max05210238/CryptoBar/docs/images/product/boot_screen_blue_led.jpeg

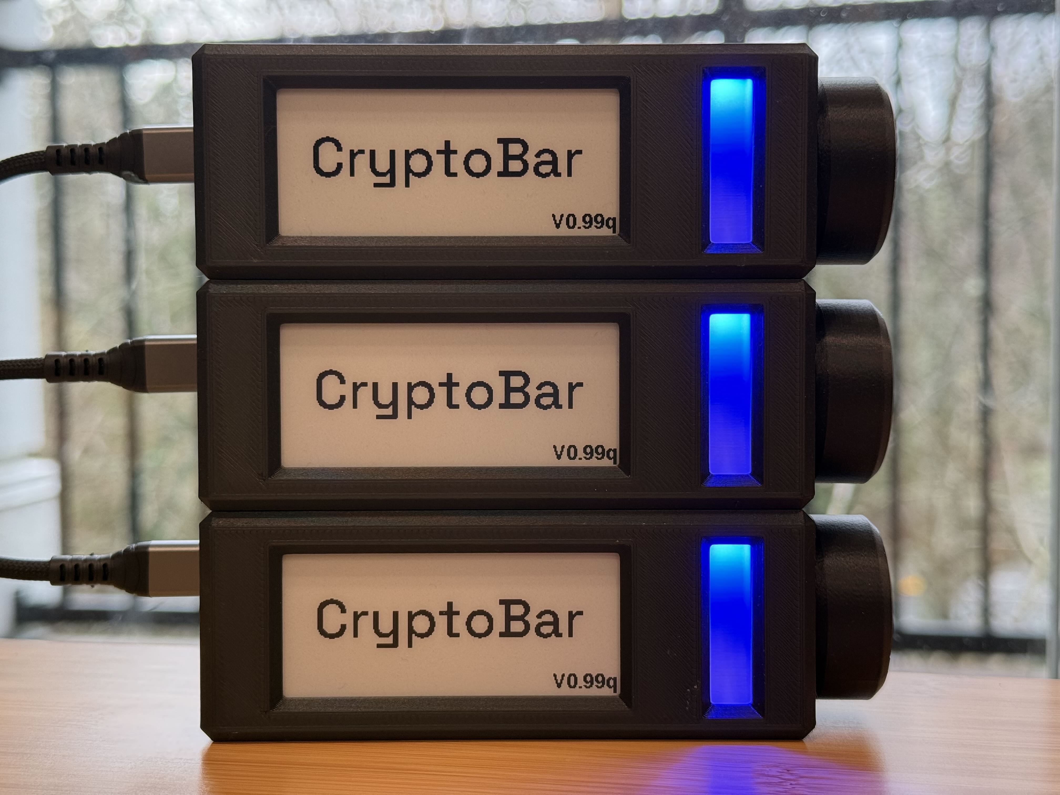
docs/images/product/boot_screen_blue_led.jpeg
