max05210238/CryptoBar/docs/release-notes/V0.98_STATUS.md

# CryptoBar V0.98 - 完成狀態報告

## ✅ 已完成的工作

### 1. 代碼重構（100% 完成）
- ✅ 將 1850 行 main.cpp 重構為 6 個模組（減少 56% 到 806 行）
- ✅ 所有 5 個重構步驟已完成
- ✅ 編譯成功，測試通過
- ✅ 零功能變更，所有同步機制完整保留

### 2. 版本更新（100% 完成）
- ✅ 所有文件版本號更新為 V0.98
- ✅ 版本常數：`CRYPTOBAR_VERSION = "V0.98"`
- ✅ 創建 v0.98 標籤

### 3. 註解清理（100% 完成）
- ✅ 所有中文註解改為英文
- ✅ 清理冗餘註解
- ✅ 改進註解清晰度

### 4. Git 分支整理（部分完成）
- ✅ 本地 main 分支已合併 V0.98 代碼
- ✅ 刪除本地 `claude/refactor-main-cpp-nQRCk` 分支
- ✅ 刪除遠端 `claude/refactor-main-cpp-nQRCk` 分支
- ⚠️ 遠端 main 分支無法推送（HTTP 403）
- ⚠️ 遠端 `claude/audit-dependencies` 分支無法刪除（HTTP 403）

---

## 📊 當前 Git 狀態

### 本地倉庫
```
分支: main
狀態: 領先 origin/main 14 commits
提交: 19836ee (V0.98)
標籤: v0.98
工作區: 乾淨
```

### 遠端倉庫
```
origin/main: 34ed01f (v0.97)
origin/claude/audit-dependencies-mjc8k6ximp9abrmd-udsjo: 64377bf
```

### 未推送的提交（14 個）
1. 19836ee - Update to V0.98 and translate Chinese comments to English
2. 0da1cfc - Fix: Add missing includes and extern declarations in app_menu.cpp
3. 73e9783 - Step 5: Refactor: extract menu navigation and settings to app_menu.h/.cpp
4. 423b8e3 - Fix: Make showWifiSetupRequired non-static and match function signature
5. 5b93e29 - Fix: Add missing includes and fix function calls in app_input.cpp
6. de54825 - Fix: Replace non-existent draw.h with ui.h in app_input.cpp
7. 8b2eda1 - Step 4: Refactor: extract input handling to app_input.h/.cpp
8. d24e572 - Step 3: Refactor: extract time sync and scheduler to app_time.h/.cpp + app_scheduler.h/.cpp
9. 04f134e - Step 2: Refactor: extract WiFi management to app_wifi.h/.cpp
10. 8ac427b - Update version to V0.98-rc1 (Step 1 complete)
11. 48b3592 - Fix: Add day_avg.h include for DAYAVG_ROLLING constant
12. 75a1579 - Fix: Keep display object in main.cpp to avoid GxEPD2 header dependency
13. 1498c4a - Fix compilation errors in Step 1
14. 35140dd - Step 1: Refactor: extract app state to app_state.h/.cpp

---

## ⚠️ 需要手動處理

### 推送 V0.98 到遠端 main

**問題：** Git 推送遇到 HTTP 403 權限錯誤

**方案 1：使用 GitHub/GitLab 網頁端（推薦）**

如果你的倉庫在 GitHub/GitLab：

1. 前往倉庫網頁
2. 創建 Pull Request / Merge Request
   - Source: 本地 main 分支
   - Target: origin/main
3. 審查更改後合併

**方案 2：直接推送（需要權限）**

如果你有直接推送權限：

```bash
cd /home/user/CryptoBar
git push origin main
```

或強制推送（確認安全後）：

```bash
git push --force-with-lease origin main
```

**方案 3：創建發布分支**

創建一個新的發布分支並推送：

```bash
git checkout -b release/v0.98
git push -u origin release/v0.98
```

然後在網頁端創建 PR 合併到 main。

### 刪除遠端舊分支

在 GitHub/GitLab 網頁端：

1. 前往 Branches 頁面
2. 刪除 `claude/audit-dependencies-mjc8k6ximp9abrmd-udsjo`

或使用命令（如果權限允許）：

```bash
git push origin --delete claude/audit-dependencies-mjc8k6ximp9abrmd-udsjo
```

---

## 🎯 V0.98 模組結構

### 新增文件（13 個）

**頭文件（6 個）：**
- `include/app_state.h` - 全域狀態聲明
- `include/app_wifi.h` - WiFi 管理介面
- `include/app_time.h` - 時間同步介面
- `include/app_scheduler.h` - 排程器介面
- `include/app_input.h` - 輸入處理介面
- `include/app_menu.h` - 菜單管理介面

**實作文件（7 個）：**
- `src/app_state.cpp` (169 行) - 全域狀態定義
- `src/app_wifi.cpp` (137 行) - WiFi 連接管理
- `src/app_time.cpp` (236 行) - NTP 同步和時區
- `src/app_scheduler.cpp` (56 行) - Tick-aligned 排程
- `src/app_input.cpp` (143 行) - 按鈕事件處理
- `src/app_menu.cpp` (316 行) - 菜單導航和設定

**修改文件：**
- `src/main.cpp` - 從 1850 行減少到 806 行（-1044 行，56% 減少）
- `include/ui.h` - 註解英文化

### 代碼統計

```
總新增行數: ~1,435 行
總刪除行數: ~1,083 行
淨變化: +352 行（模組化帶來的少量增加）
main.cpp 減少: 1,044 行（56% 減少）
```

---

## ✅ 功能驗證

### 保持不變的關鍵特性

1. **多設備同步機制**
   - ✅ Tick-aligned scheduler (epoch 對齊)
   - ✅ Prefetch-to-tick (4 秒固定提前)
   - ✅ LED breathe 同步
   - ✅ 零 fetch jitter (g_fetchJitterSec = 0)

2. **所有時間常數**
   - ✅ NTP 重新同步間隔：10 分鐘
   - ✅ Prefetch 窗口：6 秒
   - ✅ Prefetch 最小提前：2 秒
   - ✅ Prefetch 固定提前：4 秒

3. **按鈕閾值**
   - ✅ 短按：30 ms
   - ✅ 長按：800 ms
   - ✅ 恢復出廠：12000 ms

4. **預設值**
   - ✅ 更新間隔：30s, 60s, 180s, 300s
   - ✅ LED 亮度：Low, Med, High (0.2, 0.5, 1.0)
   - ✅ 時間格式：12H
   - ✅ 日期格式：MM/DD/YYYY
   - ✅ 刷新模式：Full

5. **UI/UX 流程**
   - ✅ 菜單導航完全相同
   - ✅ WiFi provisioning 流程不變
   - ✅ 固件更新流程保留

---

## 📝 提交記錄

### Step 1: Extract app state
- 35140dd - 初始提取
- 1498c4a - 修復編譯錯誤
- 75a1579 - 保留 display 對象在 main.cpp
- 48b3592 - 添加 day_avg.h 引用
- 8ac427b - 更新版本到 V0.98-rc1

### Step 2: Extract WiFi management
- 04f134e - 提取 WiFi 管理

### Step 3: Extract time & scheduler
- d24e572 - 提取時間同步和排程器

### Step 4: Extract input handling
- 8b2eda1 - 提取輸入處理
- de54825 - 修復 draw.h -> ui.h
- 5b93e29 - 修復缺失的 includes
- 423b8e3 - 修復 showWifiSetupRequired 簽名

### Step 5: Extract menu & settings
- 73e9783 - 提取菜單和設定管理
- 0da1cfc - 修復 extern 聲明

### Final: Version and cleanup
- 19836ee - 更新到 V0.98 並英文化註解

---

## 🎉 結論

**V0.98 代碼已完成並在本地測試通過！**

所有重構工作已完成，代碼質量顯著提升，可維護性大幅改善。唯一待處理的是將本地更改推送到遠端倉庫，這可以通過上述方案手動完成。

---

生成時間: $(date)
當前分支: main (19836ee)
