max05210238/CryptoBar/src/app_state.cpp

// CryptoBar V0.99t (Non-blocking Network)
// app_state.cpp - Global application state definitions
#include "app_state.h"
#include "day_avg.h"  // for DAYAVG_ROLLING constant

// ==================== Version =====================
const char* CRYPTOBAR_VERSION = "V0.99t (Non-blocking Network)";

// Get short version string (e.g., "V0.99s" from "V0.99s (VFD Display Support)")
const char* getShortVersion() {
  static char shortVersion[16];
  const char* spacePos = strchr(CRYPTOBAR_VERSION, ' ');
  if (spacePos) {
    size_t len = spacePos - CRYPTOBAR_VERSION;
    if (len > sizeof(shortVersion) - 1) len = sizeof(shortVersion) - 1;
    strncpy(shortVersion, CRYPTOBAR_VERSION, len);
    shortVersion[len] = '\0';
  } else {
    strncpy(shortVersion, CRYPTOBAR_VERSION, sizeof(shortVersion) - 1);
    shortVersion[sizeof(shortVersion) - 1] = '\0';
  }
  return shortVersion;
}

// ==================== Display Type Detection =====================
#include "display_interface.h"

DisplayType g_displayType = DISPLAY_UNKNOWN;
DisplayInterface* g_display = nullptr;

// ==================== Constants =====================

// Screen layout
const int SYMBOL_PANEL_WIDTH = 90;

// NTP
const char* NTP_SERVER_1 = "pool.ntp.org";
const char* NTP_SERVER_2 = "time.nist.gov";

// LED brightness presets
const float BRIGHTNESS_PRESETS[] = { 0.2f, 0.5f, 1.0f };
const char* BRIGHTNESS_LABELS[]  = { "Low", "Med", "High" };

// VFD brightness presets (V0.99s)
// Values: 0-255 (PT6302 VFD controller range)
// 0 = Auto (time-based brightness control)
const uint8_t VFD_BRIGHTNESS_PRESETS[] = { 0, 64, 128, 179, 255 };
const char* VFD_BRIGHTNESS_LABELS[]    = { "Auto", "Low", "Med", "High", "Max" };

// Update frequency presets
// V0.99s: 1min, 3min, 5min, 10min (4 presets, fixed array bounds bug)
// Recommended: 3min for 1-3 devices, 5min for 4+ devices on same network
const uint32_t UPDATE_PRESETS_MS[] = {
  60UL * 1000UL,   // 1min
  180UL * 1000UL,  // 3min (default, recommended)
  300UL * 1000UL,  // 5min
  600UL * 1000UL   // 10min
};
const char* UPDATE_PRESET_LABELS[] = { "1m", "3m", "5m", "10m" };

// Date format labels
const char* DATE_FORMAT_LABELS[DATE_FORMAT_COUNT] = {
  "MM/DD/YYYY",
  "DD/MM/YYYY",
  "YYYY-MM-DD"
};

// Date/Time size labels
const char* DTSIZE_LABELS[] = { "Small", "Large" };

// ==================== Refresh Mode =====================
int g_refreshMode = 1;
const char* REFRESH_MODE_LABELS[] = { "Partial", "Full" };

// ==================== Display Currency (Multi-currency) =====================
// V0.99f: Extended to support 9 currencies
int   g_displayCurrency = (int)CURR_USD;

// Exchange rates: USD -> other currencies
// Index matches DisplayCurrency enum (0=USD, 1=TWD, 2=EUR, ...)
double g_usdToRate[CURR_COUNT] = {
  1.0,    // USD (always 1.0)
  32.0,   // TWD (default fallback)
  0.95,   // EUR (default fallback)
  0.79,   // GBP (default fallback)
  1.38,   // CAD (default fallback)
  149.0,  // JPY (default fallback)
  1350.0, // KRW (default fallback)
  1.35,   // SGD (default fallback)
  1.54    // AUD (default fallback)
};

bool  g_fxValid         = false;
time_t g_nextFxUpdateUtc = 0;

// Backward compatibility: g_usdToTwd points to TWD rate
double& g_usdToTwd = g_usdToRate[CURR_TWD];

// ==================== Global Variables =====================

// V0.99m: API source tracking (updated by network.cpp)
const char* g_currentPriceApi = "Paprika";      // Default: CoinPaprika
const char* g_currentHistoryApi = "CoinGecko";  // Default: CoinGecko

uint32_t g_updateIntervalMs = UPDATE_INTERVAL_MS;

// Refresh statistics
uint16_t g_partialRefreshCount = 0;

// LED / update / coin settings index
int   g_brightnessPresetIndex = 1;
float g_ledBrightness         = BRIGHTNESS_PRESETS[1];
int    g_vfdBrightnessPresetIndex = 3;  // V0.99s: Default to "High" (70%)
uint8_t g_vfdBrightness         = VFD_BRIGHTNESS_PRESETS[3];  // 179
int g_updatePresetIndex  = 0;
int g_currentCoinIndex   = 0;
int g_dateFormatIndex    = DATE_MM_DD_YYYY;
int g_timeFormat         = TIME_12H;
int g_dtSize             = 1;
int g_timezoneIndex      = DEFAULT_TIMEZONE_INDEX;
uint8_t g_dayAvgMode = DAYAVG_ROLLING;

// Timezone key presence flags
bool g_tzIndexKeyPresent = false;
bool g_tzIndexKeyPresentAtBoot = false;
bool g_bootFlagsInit = false;
bool g_tzAutoAttempted   = false;

// UI state
UiMode g_uiMode = UI_MODE_NORMAL;

// Main menu & timezone submenu index
int g_menuIndex    = 0;
int g_menuTopIndex = 0;
int g_tzMenuIndex    = DEFAULT_TIMEZONE_INDEX;
int g_tzMenuTopIndex = 0;

// Coin submenu state
int g_coinMenuIndex    = 0;
int g_coinMenuTopIndex = 0;

// Currency submenu state (V0.99f)
int g_currencyMenuIndex    = 0;
int g_currencyMenuTopIndex = 0;

// Update interval submenu state (V0.99r)
int g_updateMenuIndex    = 0;
int g_updateMenuTopIndex = 0;

// Encoder button state
bool          g_lastEncSw       = HIGH;
unsigned long g_encPressStart   = 0;

// Encoder ISR capture
volatile int g_encStepAccum = 0;
portMUX_TYPE g_encMux = portMUX_INITIALIZER_UNLOCKED;

// UI redraw throttling
bool g_menuDirty = false;
bool g_tzDirty   = false;
bool g_coinDirty = false;
bool g_currencyDirty = false;  // V0.99f
bool g_updateDirty   = false;  // V0.99r
uint32_t g_lastUiDrawMs = 0;
const uint32_t UI_DRAW_MIN_MS = 120;

// Time / price state
unsigned long lastUpdate = 0;

// ==================== Tick-aligned update scheduler =====================
const time_t TIME_VALID_MIN_UTC = 1600000000;
bool   g_timeValid      = false;
time_t g_nextUpdateUtc  = 0;

// Prefetch-to-tick
// V0.99o: Increased minimum lead time to 6s for better API response tolerance
const uint32_t PREFETCH_WINDOW_SEC   = 6;
const uint32_t PREFETCH_MIN_LEAD_SEC = 6;   // Increased from 2s to 6s
const uint32_t PREFETCH_FIXED_LEAD_SEC = 6; // Increased from 4s to 6s
uint32_t g_fetchJitterSec = 0;
bool   g_prefetchValid  = false;
time_t g_prefetchForUtc = 0;
double g_prefetchPrice  = 0.0;
double g_prefetchChange = 0.0;

double g_lastPriceUsd   = 0.0;
double g_lastChange24h  = 0.0;
bool   g_lastPriceOk    = false;

// Previous day average reference price
double g_prevDayRefPrice   = 0.0;
bool   g_prevDayRefValid   = false;

// 7pm ET cycle state
bool   g_cycleInit     = false;
time_t g_cycleStartUtc = 0;
time_t g_cycleEndUtc   = 0;

// Local timezone offset (seconds)
int32_t g_localUtcOffsetSec = 0;

// Chart samples
ChartSample g_chartSamples[MAX_CHART_SAMPLES];
int         g_chartSampleCount = 0;

// e-paper display (defined in main.cpp)

// ==================== WiFi credentials (stored in NVS) =====================
String g_wifiSsid;
String g_wifiPass;
bool   g_hasWifiCreds = false;

// ==================== WiFi runtime reconnect guards =====================
bool     g_wifiEverConnected = false;
uint32_t g_nextRuntimeReconnectMs = 0;
uint8_t  g_runtimeReconnectBatch = 0;
const uint8_t  RUNTIME_RECONNECT_ATTEMPTS = 3;
const uint32_t RUNTIME_RECONNECT_TIMEOUT_MS = 10000;
const uint32_t RUNTIME_RECONNECT_BACKOFF_MS = 30000;

AppState g_appState = APP_STATE_RUNNING;

uint32_t g_staConnectStartMs = 0;
const uint32_t STA_CONNECT_TIMEOUT_MS = 30000;

// Partial refresh limit
const uint16_t PARTIAL_REFRESH_LIMIT = 20;

// ==================== Periodic NTP resync =====================
const uint32_t NTP_RESYNC_INTERVAL_SEC = 10UL * 60UL;
volatile bool   g_ntpEventPending = false;
volatile int64_t g_ntpEventUtc = 0;
portMUX_TYPE    g_ntpMux = portMUX_INITIALIZER_UNLOCKED;
time_t g_nextNtpResyncUtc = 0;

// ==================== Independent Time Refresh (V0.99q) =====================
time_t g_nextTimeRefreshUtc = 0;
bool   g_timeRefreshEnabled = true;
