max05210238/CryptoBar/src/app_menu.cpp

// CryptoBar V0.99t (Non-blocking Network)
// app_menu.cpp - Menu navigation and settings management

#include <Arduino.h>
#include <WiFi.h>
#include "app_menu.h"
#include "app_state.h"
#include "app_wifi.h"
#include "app_time.h"
#include "app_scheduler.h"
#include "settings_store.h"
#include "led_status.h"
#include "coins.h"
#include "day_avg.h"
#include "network.h"
#include "network_task.h"  // V0.99t: Non-blocking network operations
#include "ui.h"
#include "display_vfd.h"  // V0.99s: For VFD menu items

// Forward declarations for functions that remain in main.cpp
extern const CoinInfo& currentCoin();
extern const char* dayAvgModeLabel(uint8_t mode);
extern void updateAvgLineReference(time_t nowUtc);
extern void updateEtCycle();
extern void bootstrapHistoryFromKrakenOHLC();
extern void updateLedForPrice(float change24h, bool priceOk);
extern unsigned long lastUpdate;  // from main.cpp

// ==================== Settings Management =====================

void loadSettings() {
  StoredSettings st;
  settingsStoreLoad(st);

 // Whether tzIndex was explicitly stored in NVS. Used for one-time Auto TZ.
  g_tzIndexKeyPresent = settingsStoreHasTzIndex();
  if (!g_bootFlagsInit) {
    g_tzIndexKeyPresentAtBoot = g_tzIndexKeyPresent;
    g_bootFlagsInit = true;
  }

  int upd   = st.updPreset;
  int bri   = st.briPreset;
  int vfdBri = st.vfdBriPreset;  // V0.99s: VFD brightness
  int coin  = coinIndexFromTicker(st.coinTicker.c_str());
  int tFmt  = st.timeFmt;
  int dFmt  = st.dateFmt;
  int dtSz  = st.dtSize;
  int tzIdx = st.tzIndex;
  int dayLn = st.dayAvg;
  int rf    = st.rfMode;

  int updCount   = UPDATE_PRESETS_COUNT;
  int briCount   = BRIGHTNESS_PRESETS_COUNT;
  int vfdBriCount = VFD_BRIGHTNESS_PRESETS_COUNT;

  if (upd < 0 || upd >= updCount) upd = 0;
  if (bri < 0 || bri >= briCount) bri = 1;
  if (vfdBri < 0 || vfdBri >= vfdBriCount) vfdBri = 3;  // Default: High
  if (coin < 0 || coin >= coinCount()) coin = coinIndexFromTicker(coinDefault().ticker);
  if (tFmt < 0 || tFmt > TIME_12H) tFmt = TIME_12H;
  if (dFmt < 0 || dFmt >= DATE_FORMAT_COUNT) dFmt = DATE_MM_DD_YYYY;
  if (dtSz < 0 || dtSz > 1) dtSz = 1;
  if (tzIdx < 0 || tzIdx >= TIMEZONE_COUNT) tzIdx = DEFAULT_TIMEZONE_INDEX;
  if (dayLn < 0 || dayLn > 2) dayLn = DAYAVG_ROLLING;
  if (rf < 0 || rf > 1) rf = 1;

  g_updatePresetIndex     = upd;
  g_updateIntervalMs      = UPDATE_PRESETS_MS[g_updatePresetIndex];
  g_brightnessPresetIndex = bri;
  g_ledBrightness         = BRIGHTNESS_PRESETS[g_brightnessPresetIndex];
  ledStatusSetMasterBrightness(g_ledBrightness);
  g_vfdBrightnessPresetIndex = vfdBri;  // V0.99s: VFD brightness
  g_vfdBrightness         = VFD_BRIGHTNESS_PRESETS[g_vfdBrightnessPresetIndex];
  g_currentCoinIndex      = coin;
  g_timeFormat            = tFmt;
  g_dateFormatIndex       = dFmt;
  g_dtSize                = dtSz;
  g_timezoneIndex         = tzIdx;
  g_dayAvgMode          = (uint8_t)dayLn;
  g_refreshMode           = rf;

  g_displayCurrency = st.dispCur;
  if (g_displayCurrency < 0 || g_displayCurrency >= (int)CURR_COUNT) g_displayCurrency = (int)CURR_USD;
  applyTimezone();

  Serial.printf("[Settings] Loaded: coin=%s, upd=%s, LED=%s, timeFmt=%s, date=%s, dtSize=%s, tz=%s, dayAvg=%s, refresh=%s, cur=%s\n",
                currentCoin().ticker,
                UPDATE_PRESET_LABELS[g_updatePresetIndex],
                BRIGHTNESS_LABELS[g_brightnessPresetIndex],
                (g_timeFormat == TIME_24H ? "24h" : "12h"),
                DATE_FORMAT_LABELS[g_dateFormatIndex],
                DTSIZE_LABELS[g_dtSize],
                TIMEZONES[g_timezoneIndex].label,
                dayAvgModeLabel(g_dayAvgMode),
                REFRESH_MODE_LABELS[g_refreshMode],
                CURRENCY_INFO[g_displayCurrency].code);
}

void saveSettings() {
  StoredSettings st;
  st.updPreset = g_updatePresetIndex;
  st.briPreset = g_brightnessPresetIndex;
  st.vfdBriPreset = g_vfdBrightnessPresetIndex;  // V0.99s: VFD brightness
  st.coinTicker = String(currentCoin().ticker);
  st.timeFmt   = g_timeFormat;
  st.dateFmt   = g_dateFormatIndex;
  st.dtSize    = g_dtSize;
  st.tzIndex   = g_timezoneIndex;
  st.dayAvg    = (int)g_dayAvgMode;
  st.rfMode    = g_refreshMode;
  st.dispCur   = g_displayCurrency;

  settingsStoreSave(st);

  Serial.printf("[Settings] Saved: coin=%s, upd=%s, LED=%s, timeFmt=%s, date=%s, dtSize=%s, tz=%s, dayAvg=%s, refresh=%s, cur=%s\n",
                currentCoin().ticker,
                UPDATE_PRESET_LABELS[g_updatePresetIndex],
                BRIGHTNESS_LABELS[g_brightnessPresetIndex],
                (g_timeFormat == TIME_24H ? "24h" : "12h"),
                DATE_FORMAT_LABELS[g_dateFormatIndex],
                DTSIZE_LABELS[g_dtSize],
                TIMEZONES[g_timezoneIndex].label,
                dayAvgModeLabel(g_dayAvgMode),
                REFRESH_MODE_LABELS[g_refreshMode],
                CURRENCY_INFO[g_displayCurrency].code);
}

// ==================== Menu Navigation =====================

void leaveMenu() {
  g_uiMode = UI_MODE_NORMAL;
  Serial.println("[Menu] Exit to main");

  // V0.99s: Use display interface for both e-ink and VFD
  if (g_display) {
    g_display->drawMainScreen(true);
  } else {
    // Fallback to e-ink legacy function
    drawMainScreen(g_lastPriceUsd, g_lastChange24h, true);
  }

  g_partialRefreshCount = 0;
  lastUpdate = millis();
}

void enterMenu() {
  g_uiMode       = UI_MODE_MENU;
  g_menuIndex    = 0;
  g_menuTopIndex = 0;
  Serial.println("[Menu] Enter");

  // V0.99s: Use display interface for both e-ink and VFD
  if (g_displayType == DISPLAY_VFD && g_display) {
    g_display->drawMenuScreen();
  } else {
    // E-ink: use legacy UI function
    drawMenuScreen(true);
  }
}

void enterTimezoneSubmenu() {
  g_uiMode         = UI_MODE_TZ_SUB;
 // g_tzMenuIndex is a DISPLAY position (UTC-ordered), not the raw tzIndex.
  g_tzMenuIndex    = tzDisplayPosFromTzIndex(g_timezoneIndex);
  g_tzMenuTopIndex = max(0, g_tzMenuIndex - 2);
  Serial.println("[Menu] Enter TZ submenu");
  drawTimezoneMenu(false);  // Partial refresh
}

// ==================== Menu Item Handlers =====================

void handleTimezoneSelect() {
 // g_tzMenuIndex is a DISPLAY position (UTC-ordered)
  g_timezoneIndex = tzIndexFromDisplayPos(g_tzMenuIndex);
  applyTimezone();
  saveSettings();
  Serial.printf("[Menu] Timezone -> %s (UTC%+d)\n", TIMEZONES[g_timezoneIndex].label, (int)TIMEZONES[g_timezoneIndex].utcOffsetHours);

  g_uiMode = UI_MODE_MENU;
  if (g_displayType == DISPLAY_VFD && g_display) {
    g_display->drawMenuScreen();
  } else {
    drawMenuScreen(false);  // Partial refresh
  }
}

void handleCoinSelect() {
  g_currentCoinIndex = g_coinMenuIndex;
  saveSettings();
  Serial.printf("[Menu] Coin -> %s (index=%d)\n",
                currentCoin().ticker, g_currentCoinIndex);

  // V0.99t: Reset chart / cycle state (non-blocking)
  g_chartSampleCount = 0;
  g_cycleInit        = false;
  g_lastPriceOk      = false;  // Trigger "Loading..." display
  updateEtCycle();

  // V0.99t: Queue async network requests (non-blocking)
  // Network task will fetch history and price in background
  networkTaskRequestHistory(g_currentCoinIndex);
  networkTaskRequestPrice(g_currentCoinIndex);

  // Return to menu immediately (no waiting for network)
  g_uiMode = UI_MODE_MENU;
  if (g_displayType == DISPLAY_VFD && g_display) {
    g_display->drawMenuScreen();
  } else {
    drawMenuScreen(false);  // Partial refresh
  }
}

void handleCurrencySelect() {
  // V0.99f: Apply selected currency and trigger FX update if needed
  g_displayCurrency = g_currencyMenuIndex;

  // Validate range
  if (g_displayCurrency < 0 || g_displayCurrency >= (int)CURR_COUNT) {
    g_displayCurrency = (int)CURR_USD;
  }

  Serial.printf("[Menu] Currency -> %s-%s\n",
                CURRENCY_INFO[g_displayCurrency].symbol,
                CURRENCY_INFO[g_displayCurrency].code);

  // If switching to non-USD currency, trigger immediate FX update
  if (g_displayCurrency != (int)CURR_USD) {
    g_nextFxUpdateUtc = 0;
  }

  saveSettings();

  // Return to main menu
  g_uiMode = UI_MODE_MENU;
  if (g_displayType == DISPLAY_VFD && g_display) {
    g_display->drawMenuScreen();
  } else {
    drawMenuScreen(false);
  }
}

void handleUpdateIntervalSelect() {
  // V0.99r: Apply selected update interval (only when user confirms selection)
  g_updatePresetIndex = g_updateMenuIndex;

  // Validate range
  if (g_updatePresetIndex < 0 || g_updatePresetIndex >= UPDATE_PRESETS_COUNT) {
    g_updatePresetIndex = 0;
  }

  g_updateIntervalMs = UPDATE_PRESETS_MS[g_updatePresetIndex];

  Serial.printf("[Menu] Update interval -> %s\n",
                UPDATE_PRESET_LABELS[g_updatePresetIndex]);

  saveSettings();
  tickSchedulerReset("MENU_UPD");
  lastUpdate = millis();

  // Return to main menu
  g_uiMode = UI_MODE_MENU;
  if (g_displayType == DISPLAY_VFD && g_display) {
    g_display->drawMenuScreen();
  } else {
    drawMenuScreen(false);
  }
}

void handleMenuSelect() {
  // V0.99s: Handle VFD-specific menu items (9 items instead of 13)
  if (g_displayType == DISPLAY_VFD) {
    switch (g_menuIndex) {
      case VFD_MENU_COIN: {
        // Enter coin submenu
        g_uiMode           = UI_MODE_COIN_SUB;
        g_coinMenuIndex    = g_currentCoinIndex;
        g_coinMenuTopIndex = 0;
        g_coinDirty        = true;
        Serial.println("[Menu] Enter COIN submenu");
        g_display->drawCoinList();
        break;
      }

      case VFD_MENU_UPDATE: {
        // Enter update interval submenu
        g_uiMode = UI_MODE_UPDATE_SUB;
        g_updateMenuIndex = g_updatePresetIndex;
        g_updateMenuTopIndex = 0;
        g_updateDirty = false;  // Will display immediately below
        Serial.println("[Menu] Enter UPDATE submenu");
        DisplayVfd* vfdDisplay = static_cast<DisplayVfd*>(g_display);
        if (vfdDisplay) {
          vfdDisplay->drawUpdateIntervalList();
        }
        break;
      }

      case VFD_MENU_LED_BRIGHTNESS: {
        // Cycle through LED brightness presets
        g_brightnessPresetIndex = (g_brightnessPresetIndex + 1) % BRIGHTNESS_PRESETS_COUNT;
        g_ledBrightness = BRIGHTNESS_PRESETS[g_brightnessPresetIndex];
        ledStatusSetMasterBrightness(g_ledBrightness);
        Serial.printf("[Menu] LED brightness -> %s\n", BRIGHTNESS_LABELS[g_brightnessPresetIndex]);
        saveSettings();
        uint8_t r=0,g_val=0,b=0;
        ledStatusGetLogicalRgb(&r, &g_val, &b);
        fadeLedTo(r, g_val, b, 5, 10);
        g_display->drawMenuScreen();
        break;
      }

      case VFD_MENU_VFD_BRIGHTNESS: {
        // Cycle through VFD brightness presets
        g_vfdBrightnessPresetIndex = (g_vfdBrightnessPresetIndex + 1) % VFD_BRIGHTNESS_PRESETS_COUNT;
        g_vfdBrightness = VFD_BRIGHTNESS_PRESETS[g_vfdBrightnessPresetIndex];

        // If Auto mode (0), let applyTimeBrightness() handle it; otherwise set fixed brightness
        if (g_vfdBrightness != 0) {
          g_display->setBrightness(g_vfdBrightness);
        }

        Serial.printf("[Menu] VFD brightness -> %s\n", VFD_BRIGHTNESS_LABELS[g_vfdBrightnessPresetIndex]);
        saveSettings();
        g_display->drawMenuScreen();
        break;
      }

      case VFD_MENU_CURRENCY: {
        // Enter currency submenu
        g_currencyMenuIndex = g_displayCurrency;
        g_uiMode = UI_MODE_CURRENCY_SUB;
        g_display->drawCurrencyList();
        break;
      }

      case VFD_MENU_TIMEZONE: {
        // Enter timezone submenu
        enterTimezoneSubmenu();
        g_display->drawTimezoneList();
        break;
      }

      case VFD_MENU_FIRMWARE: {
        // Two-step entry: show confirm screen, then long-press to enter maintenance AP
        g_uiMode = UI_MODE_FW_CONFIRM;
        Serial.println("[Menu] Firmware update (confirm)");
        DisplayVfd* vfdDisplay = static_cast<DisplayVfd*>(g_display);
        if (vfdDisplay) {
          vfdDisplay->drawFirmwareUpdateConfirmScreen(getShortVersion());
        }
        break;
      }

      case VFD_MENU_WIFI_INFO: {
        // Show WiFi info screen
        bool connected = (WiFi.status() == WL_CONNECTED);
        String mac = WiFi.macAddress();
        String ip  = connected ? WiFi.localIP().toString() : String("");
        int bars   = connected ? rssiToBars(WiFi.RSSI()) : 0;
        int ch     = connected ? WiFi.channel() : 0;

        g_uiMode = UI_MODE_WIFI_INFO;
        DisplayVfd* vfdDisplay = static_cast<DisplayVfd*>(g_display);
        if (vfdDisplay) {
          vfdDisplay->drawWifiInfoScreen(getShortVersion(), mac.c_str(), ip.c_str(), bars, ch, connected);
        }
        break;
      }

      case VFD_MENU_EXIT:
        leaveMenu();
        break;

      default:
        Serial.printf("[Menu] Unknown VFD menu index: %d\n", g_menuIndex);
        break;
    }
    return;
  }

  // E-ink menu handling (original 13-item menu)
  switch (g_menuIndex) {
    case MENU_COIN: {
 // Enter coin submenu
      g_uiMode           = UI_MODE_COIN_SUB;
      g_coinMenuIndex    = g_currentCoinIndex;
      g_coinMenuTopIndex = 0;
      g_coinDirty        = true;
      Serial.println("[Menu] Enter COIN submenu");
      drawCoinMenu(false);  // Partial refresh
      break;
    }

    case MENU_UPDATE_INTERVAL: {
      // V0.99r: Enter update interval submenu (prevents accidental data fetching)
      g_uiMode = UI_MODE_UPDATE_SUB;
      g_updateMenuIndex = g_updatePresetIndex;  // Start at current setting
      g_updateMenuTopIndex = 0;
      g_updateDirty = true;
      Serial.println("[Menu] Enter UPDATE submenu");
      drawUpdateMenu(false);  // Partial refresh
      break;
    }

    case MENU_LED_BRIGHTNESS: {
      int presetCount = BRIGHTNESS_PRESETS_COUNT;
      g_brightnessPresetIndex = (g_brightnessPresetIndex + 1) % presetCount;
      g_ledBrightness         = BRIGHTNESS_PRESETS[g_brightnessPresetIndex];
      ledStatusSetMasterBrightness(g_ledBrightness);
      Serial.printf("[Menu] LED brightness -> %s\n",
                    BRIGHTNESS_LABELS[g_brightnessPresetIndex]);
      saveSettings();
      uint8_t r=0,g=0,b=0;
      ledStatusGetLogicalRgb(&r, &g, &b);
      fadeLedTo(r, g, b, 5, 10);
      drawMenuScreen(false);
      break;
    }

    case MENU_TIME_FORMAT: {
      g_timeFormat = (g_timeFormat == TIME_24H) ? TIME_12H : TIME_24H;
      Serial.printf("[Menu] Time format -> %s\n",
                    (g_timeFormat == TIME_24H ? "24h" : "12h"));
      saveSettings();
      drawMenuScreen(false);
      break;
    }

    case MENU_DATE_FORMAT: {
      g_dateFormatIndex = (g_dateFormatIndex + 1) % DATE_FORMAT_COUNT;
      Serial.printf("[Menu] Date format -> %s\n",
                    DATE_FORMAT_LABELS[g_dateFormatIndex]);
      saveSettings();
      drawMenuScreen(false);
      break;
    }

    case MENU_DATETIME_SIZE: {
      g_dtSize = (g_dtSize == 0) ? 1 : 0;
      Serial.printf("[Menu] Date/Time size -> %s\n",
                    DTSIZE_LABELS[(g_dtSize >= 0 && g_dtSize < 2) ? g_dtSize : 1]);
      saveSettings();
      drawMenuScreen(false);
      break;
    }

    case MENU_TIMEZONE: {
      enterTimezoneSubmenu();
      break;
    }

    case MENU_REFRESH_MODE: {
      g_refreshMode = (g_refreshMode + 1) % 2;
      Serial.printf("[Menu] Refresh mode -> %s\n", REFRESH_MODE_LABELS[g_refreshMode]);
      saveSettings();
      drawMenuScreen(false);
      break;
    }

    case MENU_CURRENCY: {
      // V0.99f: Enter currency submenu
      g_currencyMenuIndex = g_displayCurrency;  // Start at current currency
      g_uiMode = UI_MODE_CURRENCY_SUB;
      drawCurrencyMenu(false);
      break;
    }

    case MENU_DAYAVG_LINE: {
      g_dayAvgMode = (uint8_t)((g_dayAvgMode + 1) % 3);
      Serial.printf("[Menu] Day avg -> %s\n", dayAvgModeLabel(g_dayAvgMode));
 // Update reference immediately so the dashed line reflects the new mode.
      updateAvgLineReference(time(nullptr));
      saveSettings();
      drawMenuScreen(false);
      break;
    }

    case MENU_FIRMWARE_UPDATE: {
 // Two-step entry: show confirm screen, then long-press to enter maintenance AP.
      g_uiMode = UI_MODE_FW_CONFIRM;
      Serial.println("[Menu] Firmware update (confirm)");
      drawFirmwareUpdateConfirmScreen(getShortVersion());
      break;
    }

    case MENU_WIFI_INFO: {
      bool connected = (WiFi.status() == WL_CONNECTED);
      String mac = WiFi.macAddress();
      String ip  = connected ? WiFi.localIP().toString() : String("");
      int bars   = connected ? rssiToBars(WiFi.RSSI()) : 0;
      int ch     = connected ? WiFi.channel() : 0;

      g_uiMode = UI_MODE_WIFI_INFO;
      drawWifiInfoScreen(getShortVersion(), mac.c_str(), ip.c_str(), bars, ch, connected);
      break;
    }

    case MENU_EXIT:
      leaveMenu();
      break;
  }
}
