max05210238/CryptoBar/src/network.cpp

#include <Arduino.h>
#include <WiFi.h>
#include <HTTPClient.h>
#include <ArduinoJson.h>
#include <time.h>
#include <string.h>

#include "config.h"
#include "app_state.h"
#include "coins.h"
#include "chart.h"
#include "day_avg.h"
#include "network.h"

// Some values were originally from config.h; these are fallback defaults
#ifndef MARKET_GMT_OFFSET_SEC
// Default: US Eastern Time UTC-5 (DST not handled)
#define MARKET_GMT_OFFSET_SEC (-5 * 3600)
#endif

#ifndef MARKET_ANCHOR_HOUR_ET
// 7pm ET
#define MARKET_ANCHOR_HOUR_ET 19
#endif

// Helper provided by main.cpp (declaration only; definition in main.cpp)
const CoinInfo& currentCoin();

// ==================== 7pm ET cycle & chart samples =====================

void updateEtCycle() {
  time_t nowUtc = time(nullptr);
  if (nowUtc <= 0) {
    Serial.println("[Cycle] time(nullptr) failed.");
    return;
  }

 // Convert to exchange time (default: ET)
  time_t nowEt = nowUtc + MARKET_GMT_OFFSET_SEC;

  time_t dayStartEt = nowEt - (nowEt % 86400);                   // Today 00:00 ET
  time_t anchorEt   = dayStartEt + MARKET_ANCHOR_HOUR_ET * 3600; // 7pm ET

  if (nowEt < anchorEt) {
 // Before today's 7pm → use yesterday's 7pm as anchor
    anchorEt -= 86400;
  }

  time_t startUtc = anchorEt - MARKET_GMT_OFFSET_SEC;
  time_t endUtc   = startUtc + 24 * 3600;

  if (!g_cycleInit || startUtc != g_cycleStartUtc) {
    g_cycleInit        = true;
    g_cycleStartUtc    = startUtc;
    g_cycleEndUtc      = endUtc;
    g_chartSampleCount = 0;
  dayAvgRollingReset();
    Serial.printf("[Cycle] New ET day: startUtc=%ld, endUtc=%ld\n",
                  (long)g_cycleStartUtc, (long)g_cycleEndUtc);
  }
}

// Internal: add a sample to chart buffer at specified UTC time
// V0.99p: Chart displays ET Cycle (7pm-7pm), not 24h rolling window
static void addChartSampleUtc(time_t sampleUtc, double price) {
  if (!g_cycleInit) {
    updateEtCycle();
    if (!g_cycleInit) return;
  }

  if (sampleUtc < g_cycleStartUtc) return;
  if (sampleUtc > g_cycleEndUtc)   sampleUtc = g_cycleEndUtc;

  float pos = float(sampleUtc - g_cycleStartUtc) /
              float(g_cycleEndUtc - g_cycleStartUtc);
  if (pos < 0.0f) pos = 0.0f;
  if (pos > 1.0f) pos = 1.0f;

  if (g_chartSampleCount < MAX_CHART_SAMPLES) {
    g_chartSamples[g_chartSampleCount].pos   = pos;
    g_chartSamples[g_chartSampleCount].price = price;
    g_chartSampleCount++;
  } else {
 // Rolling buffer: discard oldest
    for (int i = 1; i < MAX_CHART_SAMPLES; ++i) {
      g_chartSamples[i - 1] = g_chartSamples[i];
    }
    g_chartSamples[MAX_CHART_SAMPLES - 1].pos   = pos;
    g_chartSamples[MAX_CHART_SAMPLES - 1].price = price;
  }
}

// Public API: add a sample using current time
// Fixed: instead of adding a point every 30s, use 5-minute buckets (matching Kraken OHLC interval=5)
// - Within the same 5-minute bucket, only update the last price
// - Only append a new sample when crossing bucket boundaries
void addChartSampleForNow(double price) {
  time_t nowUtc = time(nullptr);
  if (nowUtc <= 0) {
    Serial.println("[Chart] time(nullptr) failed in addChartSampleForNow().");
    return;
  }

  updateEtCycle();
  if (!g_cycleInit) return;

  const int BUCKET_SEC = 5 * 60; // 5 minutes
  int bucket = (int)((nowUtc - g_cycleStartUtc) / BUCKET_SEC);
  if (bucket < 0) return;

 // Reset bucket memory when cycle rolls over to new day
  static time_t s_lastCycleStart = 0;
  static int    s_lastBucket     = -1;
  if (s_lastCycleStart != g_cycleStartUtc) {
    s_lastCycleStart = g_cycleStartUtc;
    s_lastBucket = -1;
  }

 // Same bucket: update last point, don't add new one (prevents filling 300 samples too quickly)
  if (bucket == s_lastBucket && g_chartSampleCount > 0) {
    g_chartSamples[g_chartSampleCount - 1].price = price;
    return;
  }

 // New bucket: add new point (using bucket start time)
  s_lastBucket = bucket;
  time_t bucketUtc = g_cycleStartUtc + (time_t)bucket * BUCKET_SEC;
  addChartSampleUtc(bucketUtc, price);
}

// ==================== Price fetching =====================

static bool fetchPriceFromPaprika(double& priceUsd, double& change24h) {
  const CoinInfo& coin = currentCoin();

  if (!coin.paprikaId || coin.paprikaId[0] == '\0') {
    Serial.println("[CP] No paprikaId configured for this coin.");
    return false;
  }
  if (WiFi.status() != WL_CONNECTED) {
    Serial.println("[CP] WiFi not connected.");
    return false;
  }

  HTTPClient http;
  // V0.99b: Avoid String concatenation (heap fragmentation)
  char url[128];
  snprintf(url, sizeof(url), "https://api.coinpaprika.com/v1/tickers/%s", coin.paprikaId);

  Serial.print("[CP] GET ");
  Serial.println(url);

  http.begin(url);
  http.setFollowRedirects(HTTPC_STRICT_FOLLOW_REDIRECTS);
  http.setTimeout(8000);

  int code = http.GET();
  if (code != 200) {
    Serial.printf("[CP] HTTP error: %d\n", code);
    http.end();
    return false;
  }

  String payload = http.getString();
  http.end();

 // Parse only the fields we need to keep memory usage low.
  StaticJsonDocument<128> filter;
  filter["quotes"]["USD"]["price"] = true;
  filter["quotes"]["USD"]["percent_change_24h"] = true;

  DynamicJsonDocument doc(1024);
  DeserializationError err = deserializeJson(doc, payload, DeserializationOption::Filter(filter));
  if (err) {
    Serial.printf("[CP] JSON parse error: %s\n", err.c_str());
    return false;
  }

  JsonObject usd = doc["quotes"]["USD"].as<JsonObject>();
  if (usd.isNull()) {
    Serial.println("[CP] quotes.USD missing.");
    return false;
  }

  priceUsd  = usd["price"].as<double>();
  change24h = usd["percent_change_24h"].as<double>();

  Serial.printf("[CP] %s: $%.6f (24h: %.2f%%)\n",
                coin.ticker, priceUsd, change24h);

  // V0.99m: Track successful API source
  if (priceUsd > 0.0) {
    g_currentPriceApi = "Paprika";
  }

  return (priceUsd > 0.0);
}

static bool fetchPriceFromKraken(double& priceUsd, double& change24h) {
  const CoinInfo& coin = currentCoin();

  if (!coin.krakenPair || coin.krakenPair[0] == '\0') {
    Serial.println("[Kraken] No krakenPair configured for this coin.");
    return false;
  }
  if (WiFi.status() != WL_CONNECTED) {
    Serial.println("[Kraken] WiFi not connected.");
    return false;
  }

  HTTPClient http;
  // V0.99b: Avoid String concatenation (heap fragmentation)
  char url[128];
  snprintf(url, sizeof(url), "https://api.kraken.com/0/public/Ticker?pair=%s", coin.krakenPair);

  Serial.print("[Kraken] GET ");
  Serial.println(url);

  http.begin(url);
  http.setFollowRedirects(HTTPC_STRICT_FOLLOW_REDIRECTS);
  http.setTimeout(8000);

  int code = http.GET();
  if (code != 200) {
    Serial.printf("[Kraken] HTTP error: %d\n", code);
    http.end();
    return false;
  }

  String payload = http.getString();
  http.end();

  // V0.99k: Debug - show first 300 chars of raw JSON response
  Serial.print("[Kraken] Raw JSON payload (first 300 chars): ");
  Serial.println(payload.substring(0, 300));

  StaticJsonDocument<4096> doc;
  DeserializationError err = deserializeJson(doc, payload);
  if (err) {
    Serial.printf("[Kraken] JSON parse error: %s\n", err.c_str());
    return false;
  }

  if (doc["error"].size() > 0) {
    Serial.print("[Kraken] API error: ");
    serializeJson(doc["error"], Serial);
    Serial.println();
    return false;
  }

  JsonObject result = doc["result"];
  if (result.isNull()) {
    Serial.println("[Kraken] result is null.");
    return false;
  }

  JsonObject ticker;
  for (JsonPair kv : result) {
    ticker = kv.value().as<JsonObject>();
    break;   // Only grab the first key
  }
  if (ticker.isNull()) {
    Serial.println("[Kraken] ticker missing.");
    return false;
  }

  // Kraken returns prices as STRING arrays, not numbers!
  // ticker["c"] = ["88799.70000", "0.01234567"] - [last, volume]
  // ticker["o"] = "88790.10000" - open price string

  const char* lastStr = ticker["c"][0] | "0";
  const char* openStr = ticker["o"] | "0";

  // V0.99k: Debug - show raw JSON strings
  Serial.printf("[Kraken] Raw JSON: c[0]=\"%s\", o=\"%s\"\n", lastStr, openStr);

  // Use strtod() instead of atof() for better precision control
  char* endPtr1;
  char* endPtr2;
  priceUsd = strtod(lastStr, &endPtr1);
  double open = strtod(openStr, &endPtr2);

  Serial.printf("[Kraken] Parsed: price=%.10f, open=%.10f\n", priceUsd, open);

  if (open <= 0.0) {
    change24h = 0.0;
  } else {
    change24h = (priceUsd - open) / open * 100.0;
  }

  Serial.printf("[Kraken] %s: $%.6f (24h: %.2f%%)\n",
                coin.ticker, priceUsd, change24h);

  // V0.99m: Track successful API source
  g_currentPriceApi = "Kraken";

  return true;
}

static bool fetchPriceFromBinance(double& priceUsd, double& change24h) {
  const CoinInfo& coin = currentCoin();

  if (!coin.binanceSymbol || coin.binanceSymbol[0] == '\0') {
    Serial.println("[Binance] No binanceSymbol configured for this coin.");
    return false;
  }
  if (WiFi.status() != WL_CONNECTED) {
    Serial.println("[Binance] WiFi not connected.");
    return false;
  }

  HTTPClient http;
  char url[192];
  snprintf(url, sizeof(url),
           "https://api.binance.com/api/v3/ticker/24hr?symbol=%s",
           coin.binanceSymbol);

  Serial.print("[Binance] GET ");
  Serial.println(url);

  http.begin(url);
  http.setFollowRedirects(HTTPC_STRICT_FOLLOW_REDIRECTS);
  http.setTimeout(8000);

  int code = http.GET();
  if (code != 200) {
    Serial.printf("[Binance] HTTP error: %d\n", code);
    http.end();
    return false;
  }

  String payload = http.getString();
  http.end();

  // V0.99k: Debug - show first 200 chars of raw JSON response
  Serial.print("[Binance] Raw JSON payload (first 200 chars): ");
  Serial.println(payload.substring(0, 200));

  // Parse Binance 24hr ticker response
  StaticJsonDocument<512> doc;
  DeserializationError err = deserializeJson(doc, payload);
  if (err) {
    Serial.printf("[Binance] JSON parse error: %s\n", err.c_str());
    return false;
  }

  // Check for API error
  if (doc.containsKey("code")) {
    int errCode = doc["code"].as<int>();
    const char* msg = doc["msg"] | "unknown";
    Serial.printf("[Binance] API error %d: %s\n", errCode, msg);
    return false;
  }

  // Binance returns prices as STRINGS in JSON, not numbers
  const char* lastPriceStr = doc["lastPrice"] | "0";
  const char* changePercentStr = doc["priceChangePercent"] | "0";

  // V0.99k: Debug - show raw JSON string values
  Serial.printf("[Binance] Raw JSON: price=\"%s\", change=\"%s\"\n", lastPriceStr, changePercentStr);

  // Use strtod() for string-to-double conversion with full precision
  char* endPtr1;
  char* endPtr2;
  priceUsd  = strtod(lastPriceStr, &endPtr1);
  change24h = strtod(changePercentStr, &endPtr2);

  Serial.printf("[Binance] Parsed: $%.10f (24h: %.2f%%)\n", priceUsd, change24h);
  Serial.printf("[Binance] %s: $%.6f (24h: %.2f%%)\n",
                coin.ticker, priceUsd, change24h);

  // V0.99m: Track successful API source
  if (priceUsd > 0.0) {
    g_currentPriceApi = "Binance";
  }

  return (priceUsd > 0.0);
}

static bool fetchPriceFromCoingecko(double& priceUsd, double& change24h) {
  const CoinInfo& coin = currentCoin();

  if (WiFi.status() != WL_CONNECTED) {
    Serial.println("[CG] WiFi not connected.");
    return false;
  }

 // Use registry-provided CoinGecko id when available.
  if (!coin.geckoId || coin.geckoId[0] == '\0') {
    Serial.println("[CG] No geckoId configured for this coin.");
    return false;
  }

  HTTPClient http;
  // V0.99b: Avoid String concatenation (heap fragmentation)
  // V0.99p: Added precision=full parameter to request maximum decimal places
  char url[256];
  snprintf(url, sizeof(url),
           "https://api.coingecko.com/api/v3/simple/price?ids=%s&vs_currencies=usd&include_24hr_change=true&precision=full",
           coin.geckoId);

  Serial.print("[CG] GET ");
  Serial.println(url);

  http.begin(url);
  http.setFollowRedirects(HTTPC_STRICT_FOLLOW_REDIRECTS);
  http.setTimeout(8000);

  int code = http.GET();
  if (code != 200) {
    Serial.printf("[CG] HTTP error: %d\n", code);
    http.end();
    return false;
  }

  String payload = http.getString();
  http.end();

  // V0.99p: Enhanced debug - show complete raw JSON response
  Serial.println("[CG] ========== RAW JSON RESPONSE ==========");
  Serial.println(payload);
  Serial.println("[CG] ======================================");

  StaticJsonDocument<512> doc;
  DeserializationError err = deserializeJson(doc, payload);
  if (err) {
    Serial.printf("[CG] JSON parse error: %s\n", err.c_str());
    return false;
  }

  // V0.99b: Use coin.geckoId directly instead of String temporary
  JsonObject coinObj = doc[coin.geckoId];
  if (coinObj.isNull()) {
    Serial.println("[CG] Coin id missing.");
    return false;
  }

  // CoinGecko returns prices as numbers (not strings)
  const char* rawPrice = doc[coin.geckoId]["usd"] | "null";
  const char* rawChange = doc[coin.geckoId]["usd_24h_change"] | "null";

  priceUsd  = coinObj["usd"].as<double>();
  change24h = coinObj["usd_24h_change"].as<double>();

  // V0.99k: Debug - show raw JSON and parsed values
  // V0.99p: Show up to 10 decimal places to verify precision
  Serial.printf("[CG] Raw JSON: usd=%s, change=%s\n", rawPrice, rawChange);
  Serial.printf("[CG] Parsed: $%.10f (24h: %.2f%%)\n", priceUsd, change24h);
  Serial.printf("[CG] %s: $%.10f (24h: %.2f%%)\n",
                coin.ticker, priceUsd, change24h);

  // V0.99m: Track successful API source
  g_currentPriceApi = "CoinGecko";

  return true;
}

bool fetchPrice(double& priceUsd, double& change24h) {
  if (WiFi.status() != WL_CONNECTED) {
    Serial.println("[Price] WiFi not connected.");
    return false;
  }

  // V0.99n: Prioritize CoinGecko (best aggregated market data quality)
  // CoinGecko → CoinPaprika → Kraken → Binance
  // For open-source project: only free APIs, no API keys needed
  if (fetchPriceFromCoingecko(priceUsd, change24h)) {
    return true;
  }
  Serial.println("[Price] CoinGecko failed, falling back to CoinPaprika...");

  if (fetchPriceFromPaprika(priceUsd, change24h)) {
    return true;
  }
  Serial.println("[Price] CoinPaprika failed, falling back to Kraken...");

  if (fetchPriceFromKraken(priceUsd, change24h)) {
    return true;
  }
  Serial.println("[Price] Kraken failed, falling back to Binance...");

  if (fetchPriceFromBinance(priceUsd, change24h)) {
    return true;
  }

  Serial.println("[Price] All providers failed.");
  return false;
}

// ==================== Historical OHLC bootstrap =====================

static bool bootstrapHistoryFromCoingeckoMarketChart() {
  const CoinInfo& coin = currentCoin();

  if (!coin.geckoId || coin.geckoId[0] == '\0') {
    Serial.println("[History][CG] No geckoId configured for this coin.");
    return false;
  }
  if (WiFi.status() != WL_CONNECTED) {
    Serial.println("[History][CG] WiFi not connected.");
    return false;
  }

 // Ensure 7pm ET cycle exists (still needed for Cycle mean mode).
  updateEtCycle();
  if (!g_cycleInit) {
    Serial.println("[History][CG] cycle not initialized.");
    return false;
  }

  time_t nowUtc = time(nullptr);
  if (nowUtc <= 0) {
    Serial.println("[History][CG] time(nullptr) failed.");
    return false;
  }

  // V0.99o: Restore original ET Cycle window logic
  time_t windowStartUtc = g_cycleStartUtc;
  time_t windowEndUtc   = g_cycleEndUtc;
  if (nowUtc < windowEndUtc) windowEndUtc = nowUtc;

  HTTPClient http;
  // V0.99b: Avoid String concatenation (heap fragmentation)
  char url[192];
  snprintf(url, sizeof(url),
           "https://api.coingecko.com/api/v3/coins/%s/market_chart?vs_currency=usd&days=1",
           coin.geckoId);

  Serial.print("[History][CG] GET ");
  Serial.println(url);

  http.begin(url);
  http.setFollowRedirects(HTTPC_STRICT_FOLLOW_REDIRECTS);
  http.setTimeout(8000);

  int code = http.GET();
  if (code != 200) {
    Serial.printf("[History][CG] HTTP error: %d\n", code);
    http.end();
    return false;
  }

  String payload = http.getString();
  http.end();

 // Only keep the 'prices' array to reduce memory usage.
  StaticJsonDocument<64> filter;
  filter["prices"] = true;

 // V0.99b: Reduced from 24576 to 16384 (33% reduction) to save heap
 // Filter extracts only "prices" array, reducing memory footprint
  DynamicJsonDocument doc(16384);
  DeserializationError err = deserializeJson(doc, payload, DeserializationOption::Filter(filter));
  if (err) {
    if (err == DeserializationError::NoMemory) {
      Serial.printf("[History][CG] Insufficient memory for parsing (need >16KB)\n");
      Serial.printf("[History][CG] Free heap: %u bytes\n", ESP.getFreeHeap());
    } else {
      Serial.printf("[History][CG] JSON parse error: %s\n", err.c_str());
    }
    return false;
  }

  JsonArray prices = doc["prices"].as<JsonArray>();
  if (prices.isNull()) {
    Serial.println("[History][CG] prices missing.");
    return false;
  }

  g_chartSampleCount = 0;
  dayAvgRollingReset();
  int kept = 0;

  for (JsonVariant v : prices) {
    JsonArray row = v.as<JsonArray>();
    if (row.isNull() || row.size() < 2) continue;

 // CoinGecko timestamps are milliseconds.
    long long tMs = row[0].as<long long>();
    time_t tUtc = (time_t)(tMs / 1000LL);
    double price = row[1].as<double>();
    if (price <= 0.0) continue;

 // Rolling 24h mean uses full last-day window (seeded from CoinGecko)
    dayAvgRollingAdd(tUtc, price);
    if (tUtc < windowStartUtc || tUtc > windowEndUtc) continue;
    addChartSampleUtc(tUtc, price);
    kept++;
  }

  Serial.printf("[History][CG] Kept %d samples into chart.\n", kept);

  // V0.99m: Track successful history API source
  if (kept > 0) {
    g_currentHistoryApi = "CoinGecko";
  }

  return (kept > 0);
}

static bool bootstrapHistoryFromBinanceKlines() {
  const CoinInfo& coin = currentCoin();

  if (!coin.binanceSymbol || coin.binanceSymbol[0] == '\0') {
    Serial.println("[History][Binance] No binanceSymbol configured for this coin.");
    return false;
  }
  if (WiFi.status() != WL_CONNECTED) {
    Serial.println("[History][Binance] WiFi not connected.");
    return false;
  }

  // Ensure 7pm ET cycle exists (still needed for Cycle mean mode)
  updateEtCycle();
  if (!g_cycleInit) {
    Serial.println("[History][Binance] cycle not initialized.");
    return false;
  }

  time_t nowUtc = time(nullptr);
  if (nowUtc <= 0) {
    Serial.println("[History][Binance] time(nullptr) failed.");
    return false;
  }

  // V0.99o: Restore original ET Cycle window logic
  time_t windowStartUtc = g_cycleStartUtc;
  time_t windowEndUtc   = g_cycleEndUtc;
  if (nowUtc < windowEndUtc) windowEndUtc = nowUtc;

  // Start time for API request
  time_t sinceUtc = windowStartUtc;

  // Convert to milliseconds for Binance API
  long long startTimeMs = (long long)sinceUtc * 1000LL;

  HTTPClient http;
  char url[256];
  snprintf(url, sizeof(url),
           "https://api.binance.com/api/v3/klines?symbol=%s&interval=5m&startTime=%lld&limit=500",
           coin.binanceSymbol, startTimeMs);

  Serial.print("[History][Binance] GET ");
  Serial.println(url);

  http.begin(url);
  http.setFollowRedirects(HTTPC_STRICT_FOLLOW_REDIRECTS);
  http.setTimeout(8000);

  int code = http.GET();
  if (code != 200) {
    Serial.printf("[History][Binance] HTTP error: %d\n", code);
    http.end();
    return false;
  }

  String payload = http.getString();
  http.end();

  Serial.printf("[History][Binance] Payload length: %d bytes\n", payload.length());

  // Parse klines data
  DynamicJsonDocument doc(32768);
  DeserializationError err = deserializeJson(doc, payload);
  if (err) {
    if (err == DeserializationError::NoMemory) {
      Serial.printf("[History][Binance] Insufficient memory for parsing (need >32KB)\n");
      Serial.printf("[History][Binance] Free heap: %u bytes\n", ESP.getFreeHeap());
    } else {
      Serial.printf("[History][Binance] JSON parse error: %s\n", err.c_str());
    }
    return false;
  }

  // Check for API error
  if (doc.containsKey("code")) {
    int errCode = doc["code"].as<int>();
    const char* msg = doc["msg"] | "unknown";
    Serial.printf("[History][Binance] API error %d: %s\n", errCode, msg);
    return false;
  }

  JsonArray klines = doc.as<JsonArray>();
  if (klines.isNull()) {
    Serial.println("[History][Binance] klines array missing.");
    return false;
  }

  Serial.printf("[History][Binance] Klines raw size: %u\n", (unsigned)klines.size());

  g_chartSampleCount = 0;
  dayAvgRollingReset();
  int kept = 0;

  for (JsonVariant v : klines) {
    JsonArray row = v.as<JsonArray>();
    if (row.isNull() || row.size() < 5) continue;

    // Binance kline format: [openTime(ms), open, high, low, close, volume, ...]
    long long tMs = row[0].as<long long>();
    time_t tUtc = (time_t)(tMs / 1000LL);
    const char* closeStr = row[4] | "0";
    double closePrice = atof(closeStr);

    if (closePrice <= 0.0) continue;

    // V0.99o: Rolling 24h mean uses full last-day window
    dayAvgRollingAdd(tUtc, closePrice);

    // Only add points within this cycle to the chart
    if (tUtc < windowStartUtc || tUtc > windowEndUtc) continue;
    addChartSampleUtc(tUtc, closePrice);
    kept++;
  }

  Serial.printf("[History][Binance] Kept %d samples into chart.\n", kept);
  Serial.printf("[History][Binance] g_chartSampleCount = %d\n", g_chartSampleCount);

  // V0.99m: Track successful history API source
  if (kept > 0) {
    g_currentHistoryApi = "Binance";
  }

  return (kept > 0);
}

void bootstrapHistoryFromKrakenOHLC() {
  const CoinInfo& coin = currentCoin();
  if (WiFi.status() != WL_CONNECTED) {
    Serial.println("[History] WiFi not connected, skip.");
    return;
  }

 // Ensure 7pm ET cycle is established first (still needed for Cycle mean mode)
  updateEtCycle();
  if (!g_cycleInit) {
    Serial.println("[History] cycle not initialized, abort.");
    return;
  }

  time_t nowUtc = time(nullptr);
  if (nowUtc <= 0) {
    Serial.println("[History] time(nullptr) failed.");
    return;
  }

 // V0.99o: Restore original ET Cycle window logic
  time_t windowStartUtc = g_cycleStartUtc;
  time_t windowEndUtc   = g_cycleEndUtc;
  if (nowUtc < windowEndUtc) windowEndUtc = nowUtc;

  Serial.printf("[History] ET Cycle window: %ld .. %ld\n",
                (long)windowStartUtc, (long)windowEndUtc);

  // V0.99k: Prioritize aggregated market data for history
  // Try CoinGecko first (aggregated), then Binance (single exchange) as fallback
  Serial.println("[History] Using aggregated market data (CoinGecko)...");
  if (bootstrapHistoryFromCoingeckoMarketChart()) {
    return;
  }

  Serial.println("[History] CoinGecko failed, trying Binance...");
  if (bootstrapHistoryFromBinanceKlines()) {
    return;
  }

  // If both aggregated sources fail and Kraken is available, use it
  if (!coin.krakenPair || coin.krakenPair[0] == '\0') {
    Serial.println("[History] All history sources failed.");
    return;
  }
  Serial.println("[History] Falling back to Kraken OHLC...");
  // Continue to Kraken OHLC below

 // Seed rolling 24h mean buffer with same 24h window
  dayAvgRollingReset();
  time_t sinceUtc = windowStartUtc;

  HTTPClient http;
  // V0.99b: Avoid String concatenation (heap fragmentation)
  // V0.99p: Fetch past 24h data to match chart window
  char url[192];
  snprintf(url, sizeof(url),
           "https://api.kraken.com/0/public/OHLC?pair=%s&interval=5&since=%ld",
           coin.krakenPair, (long)sinceUtc);

  Serial.print("[History] GET ");
  Serial.println(url);

  http.begin(url);
  http.setFollowRedirects(HTTPC_STRICT_FOLLOW_REDIRECTS);
  http.setTimeout(8000);

  int code = http.GET();
  if (code != 200) {
    Serial.printf("[History] HTTP error: %d\n", code);
    http.end();
    return;
  }

  String payload = http.getString();
  http.end();

  Serial.printf("[History] Payload length: %d bytes\n", payload.length());

 // V0.99b: Reduced from 49152 to 32768 (33% reduction) to save heap
 // With since= parameter, payload is filtered to current cycle only
  DynamicJsonDocument doc(32768);
  DeserializationError err = deserializeJson(doc, payload);
  if (err) {
    if (err == DeserializationError::NoMemory) {
      Serial.printf("[History] Insufficient memory for OHLC parsing (need >32KB)\n");
      Serial.printf("[History] Free heap: %u bytes\n", ESP.getFreeHeap());
    } else {
      Serial.printf("[History] JSON parse error: %s\n", err.c_str());
    }
    return;
  }

  if (doc["error"].size() > 0) {
    Serial.print("[History] API error: ");
    serializeJson(doc["error"], Serial);
    Serial.println();
    return;
  }

  JsonObject result = doc["result"];
  if (result.isNull()) {
    Serial.println("[History] result is null.");
    return;
  }

 // Kraken returns dynamic keys (pair name) + a 'last' field.
  JsonArray ohlcArr;
  for (JsonPair kv : result) {
    if (strcmp(kv.key().c_str(), "last") == 0) continue;
    ohlcArr = kv.value().as<JsonArray>();
    break;
  }
  if (ohlcArr.isNull()) {
    // V0.99g: Try Binance first, fallback to CoinGecko
    Serial.println("[History] OHLC array missing or wrong type.");
    Serial.println("[History] Trying Binance...");
    if (bootstrapHistoryFromBinanceKlines()) {
      return;
    }
    Serial.println("[History] Binance history failed, trying CoinGecko...");
    if (!bootstrapHistoryFromCoingeckoMarketChart()) {
      Serial.println("[History] CoinGecko history failed.");
    }
    return;
  }

  Serial.printf("[History] OHLC raw size: %u\n", (unsigned)ohlcArr.size());

  g_chartSampleCount = 0;
  dayAvgRollingReset();
  long minT = LONG_MAX;
  long maxT = LONG_MIN;
  int  kept = 0;

  for (JsonVariant v : ohlcArr) {
    JsonArray row = v.as<JsonArray>();
    if (row.isNull() || row.size() < 5) continue;

    long tUtc = row[0].as<long>();
    const char* closeStr = row[4] | "0";

    if (tUtc < minT) minT = tUtc;
    if (tUtc > maxT) maxT = tUtc;

 // Only add points within this cycle to the chart
    if (tUtc < windowStartUtc || tUtc > windowEndUtc) continue;

    double closePrice = atof(closeStr);
    dayAvgRollingAdd((time_t)tUtc, closePrice);
    addChartSampleUtc((time_t)tUtc, closePrice);
    kept++;
  }

  Serial.printf("[History] OHLC timestamp range UTC: %ld .. %ld\n",
                (minT == LONG_MAX ? 0 : minT),
                (maxT == LONG_MIN ? 0 : maxT));
  Serial.printf("[History] Kept %d samples into chart.\n", kept);
  Serial.printf("[History] g_chartSampleCount = %d\n", g_chartSampleCount);

  // V0.99m: Track successful history API source
  if (kept > 0) {
    g_currentHistoryApi = "Kraken";
  }
}


// ------------------------------
// FX: USD -> Multi-currency (V0.99f)
// ------------------------------
// Fetches exchange rates for all supported currencies
// Returns: true if at least one rate was successfully fetched
bool fetchExchangeRates() {
  if (WiFi.status() != WL_CONNECTED) {
    Serial.println("[FX] WiFi not connected; skip");
    return false;
  }

  // V0.99f: Primary API with fallback
  const char* urls[] = {
    "https://open.er-api.com/v6/latest/USD",        // Primary: 1500/month, 160+ currencies
    "https://api.fxratesapi.com/latest?base=USD",   // Fallback: unlimited, 170+ currencies
  };

  // Currency codes to extract
  const char* currCodes[CURR_COUNT] = {
    "USD", "TWD", "EUR", "GBP", "CAD", "JPY", "KRW", "SGD", "AUD"
  };

  for (size_t i = 0; i < sizeof(urls) / sizeof(urls[0]); i++) {
    const char* url = urls[i];
    HTTPClient http;
    http.setTimeout(8000);
    http.begin(url);

    Serial.printf("[FX] GET %s\n", url);
    int httpCode = http.GET();
    if (httpCode != HTTP_CODE_OK) {
      Serial.printf("[FX] HTTP %d\n", httpCode);
      http.end();
      continue;
    }

    String payload = http.getString();
    http.end();

    // Parse full rates object
    DynamicJsonDocument doc(8192);
    DeserializationError err = deserializeJson(doc, payload);
    if (err) {
      Serial.printf("[FX] JSON error: %s\n", err.c_str());
      continue;
    }

    JsonObject rates = doc["rates"].as<JsonObject>();
    if (rates.isNull()) {
      Serial.println("[FX] Missing rates object");
      continue;
    }

    // Extract all currency rates
    int successCount = 0;
    for (int c = 0; c < (int)CURR_COUNT; c++) {
      if (c == CURR_USD) {
        g_usdToRate[c] = 1.0;  // USD is always 1.0
        successCount++;
        continue;
      }

      double rate = rates[currCodes[c]].as<double>();
      if (rate > 0.001 && rate < 1000000.0) {
        g_usdToRate[c] = rate;
        successCount++;
        Serial.printf("[FX] USD->%s: %.6f\n", currCodes[c], rate);
      } else {
        Serial.printf("[FX] Invalid/missing rate for %s\n", currCodes[c]);
      }
    }

    if (successCount >= (int)CURR_COUNT / 2) {
      Serial.printf("[FX] Success: %d/%d rates fetched\n", successCount, (int)CURR_COUNT);
      return true;
    }
  }

  Serial.println("[FX] All FX endpoints failed");
  return false;
}

// Backward compatibility wrapper: USD -> TWD only
bool fetchUsdToTwdRate(float& outRate) {
  bool success = fetchExchangeRates();
  if (success) {
    outRate = g_usdToRate[CURR_TWD];
  }
  return success;
}
