max05210238/CryptoBar/src/vfd_font_5x7.h

// CryptoBar Retro V0.99s - 5x7 ASCII Font for VFD
// Standard 5x7 dot matrix font for pixel-level scrolling
// Each character is 5 columns × 7 rows
// Byte format: LSB = top pixel, MSB unused (only 7 bits used)
#pragma once

#include <Arduino.h>

// 5x7 ASCII font bitmap (characters 32-126)
// Each character: 5 bytes (columns), each byte = 7 pixels (rows)
const uint8_t FONT_5X7[][5] PROGMEM = {
  {0x00, 0x00, 0x00, 0x00, 0x00}, // 32: Space
  {0x00, 0x00, 0x5F, 0x00, 0x00}, // 33: !
  {0x00, 0x07, 0x00, 0x07, 0x00}, // 34: "
  {0x14, 0x7F, 0x14, 0x7F, 0x14}, // 35: #
  {0x24, 0x2A, 0x7F, 0x2A, 0x12}, // 36: $
  {0x23, 0x13, 0x08, 0x64, 0x62}, // 37: %
  {0x36, 0x49, 0x55, 0x22, 0x50}, // 38: &
  {0x00, 0x05, 0x03, 0x00, 0x00}, // 39: '
  {0x00, 0x1C, 0x22, 0x41, 0x00}, // 40: (
  {0x00, 0x41, 0x22, 0x1C, 0x00}, // 41: )
  {0x14, 0x08, 0x3E, 0x08, 0x14}, // 42: *
  {0x08, 0x08, 0x3E, 0x08, 0x08}, // 43: +
  {0x00, 0x50, 0x30, 0x00, 0x00}, // 44: ,
  {0x08, 0x08, 0x08, 0x08, 0x08}, // 45: -
  {0x00, 0x60, 0x60, 0x00, 0x00}, // 46: .
  {0x20, 0x10, 0x08, 0x04, 0x02}, // 47: /
  {0x3E, 0x51, 0x49, 0x45, 0x3E}, // 48: 0
  {0x00, 0x42, 0x7F, 0x40, 0x00}, // 49: 1
  {0x42, 0x61, 0x51, 0x49, 0x46}, // 50: 2
  {0x21, 0x41, 0x45, 0x4B, 0x31}, // 51: 3
  {0x18, 0x14, 0x12, 0x7F, 0x10}, // 52: 4
  {0x27, 0x45, 0x45, 0x45, 0x39}, // 53: 5
  {0x3C, 0x4A, 0x49, 0x49, 0x30}, // 54: 6
  {0x01, 0x71, 0x09, 0x05, 0x03}, // 55: 7
  {0x36, 0x49, 0x49, 0x49, 0x36}, // 56: 8
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
  const uint8_t* src;

  if (c < 32 || c > 126) {
    src = FONT_5X7[0];  // Use space for unsupported chars
  } else {
    src = FONT_5X7[c - 32];
  }

  // Copy 5 bytes from PROGMEM to RAM
  for (uint8_t i = 0; i < 5; i++) {
    output[i] = pgm_read_byte(&src[i]);
  }
}
